AndreiCurea/C.H.A.R.L.E.S./3D Designs/Suport Motor.stl

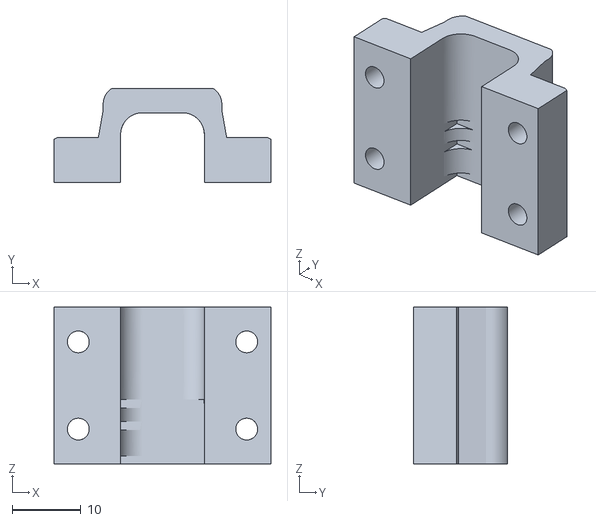
[picture p15: CAD file, 2023-12-22]
3D Designs/Suport Motor.stl
31.6 x 13.7 x 22.9
