AndreiCurea/C.H.A.R.L.E.S./3D Designs/Suport Separator Rulment.stl

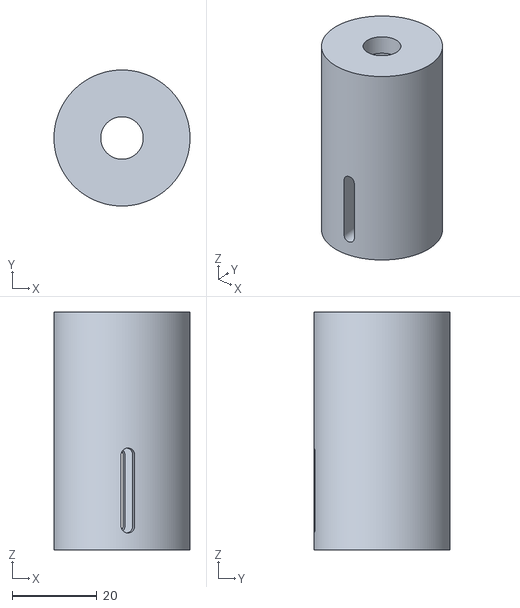
[picture p16: CAD file, 2023-12-22]
3D Designs/Suport Separator Rulment.stl
32.0 x 32.0 x 56.0
