AndreiCurea/C.H.A.R.L.E.S./3D Designs/Test_HCSR04.stl

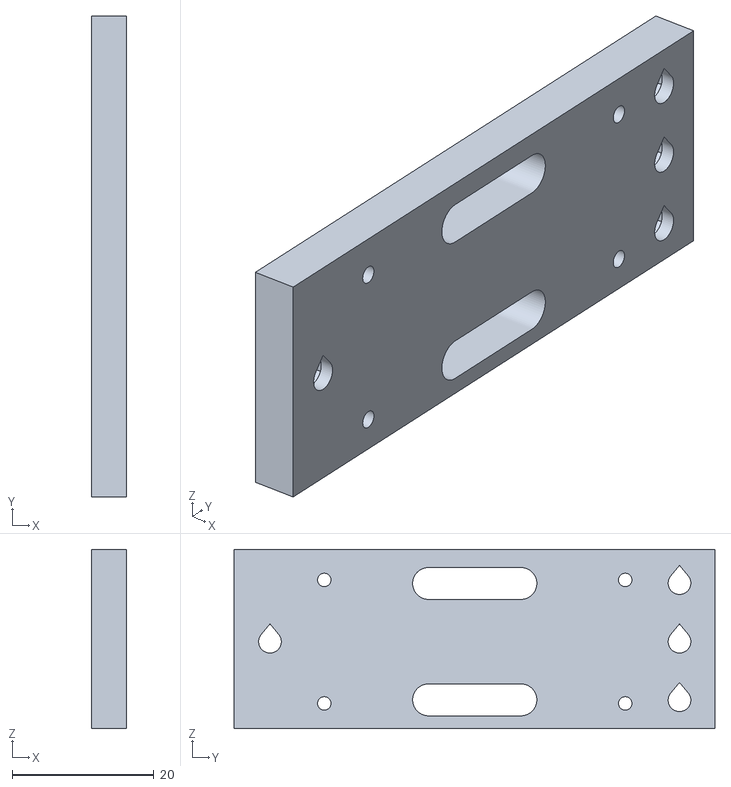
[picture p17: CAD file, 2023-12-22]
3D Designs/Test_HCSR04.stl
5.00 x 67.8 x 25.2
