AndreiCurea/C.H.A.R.L.E.S./3D Designs/Ziptie_Holder.stl

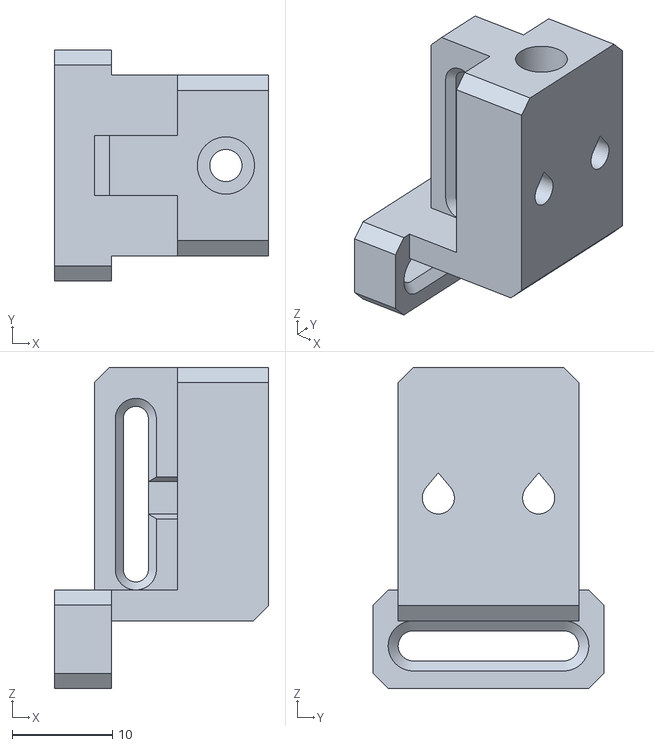
[picture p18: CAD file, 2023-12-22]
3D Designs/Ziptie_Holder.stl
21.4 x 23.0 x 32.0
