AndreiCurea/C.H.A.R.L.E.S./3D Designs/test_Gauri.stl

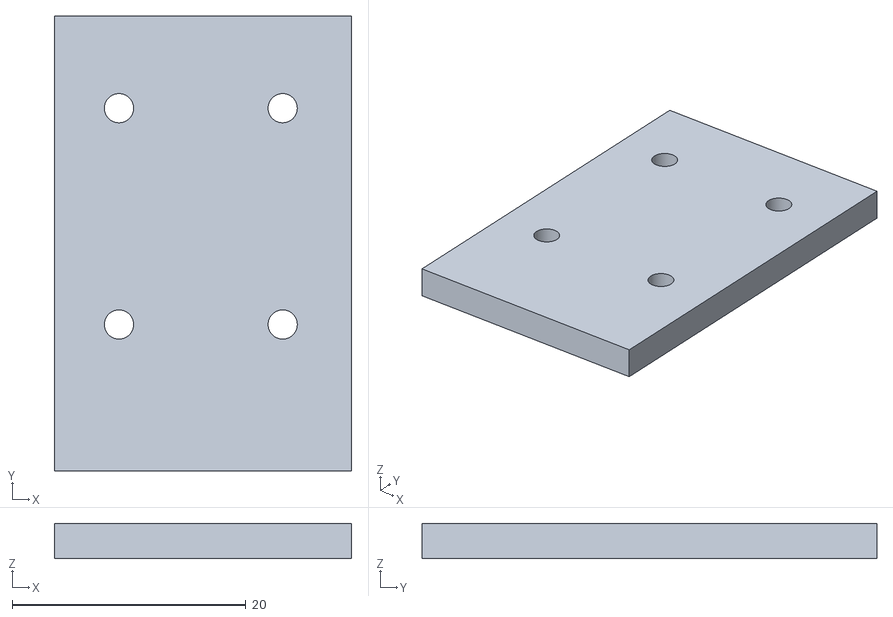
[picture p19: CAD file, 2023-12-22]
3D Designs/test_Gauri.stl
25.4 x 38.9 x 3.00
