AndreiCurea/C.H.A.R.L.E.S./3D Designs/Middle_Layer_2.stl

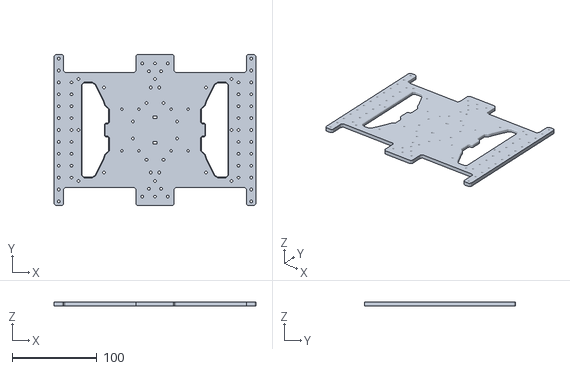
[picture p20: CAD file, 2023-12-22]
3D Designs/Middle_Layer_2.stl
237.7 x 178.0 x 5.00
