AndreiCurea/C.H.A.R.L.E.S./3D Designs/Suport_Battery_Level.stl

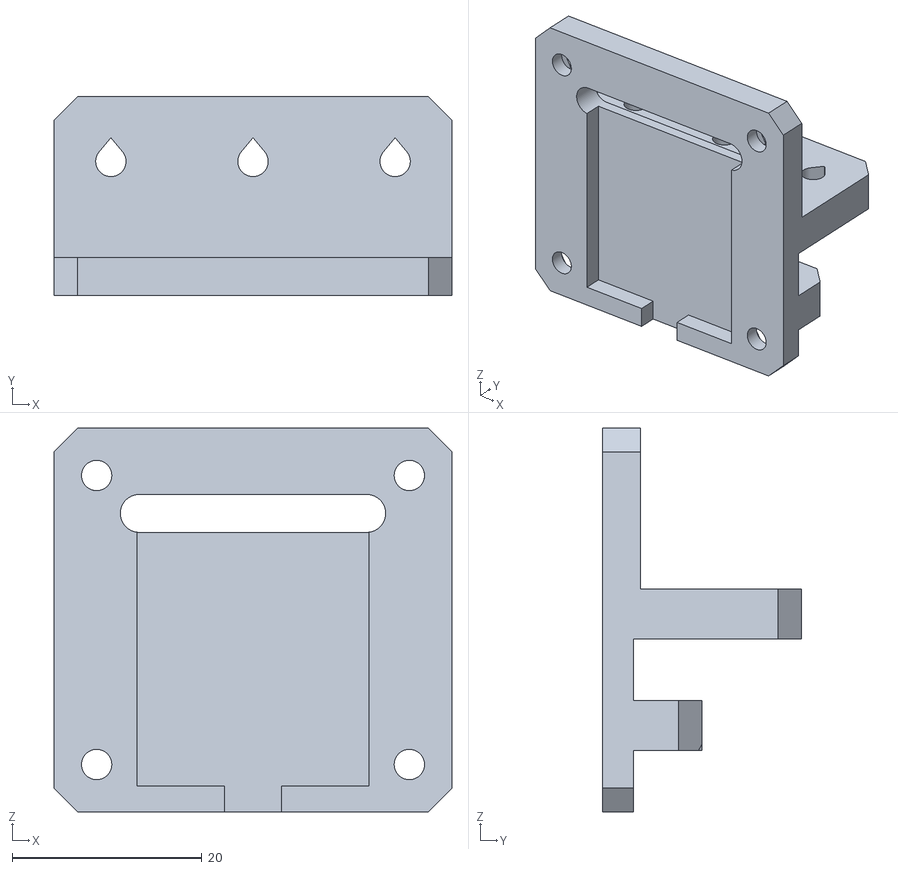
[picture p21: CAD file, 2023-12-22]
3D Designs/Suport_Battery_Level.stl
42.0 x 21.0 x 40.5
