AndreiCurea/C.H.A.R.L.E.S./3D Designs/Batt_ Conn_Dreapta.stl

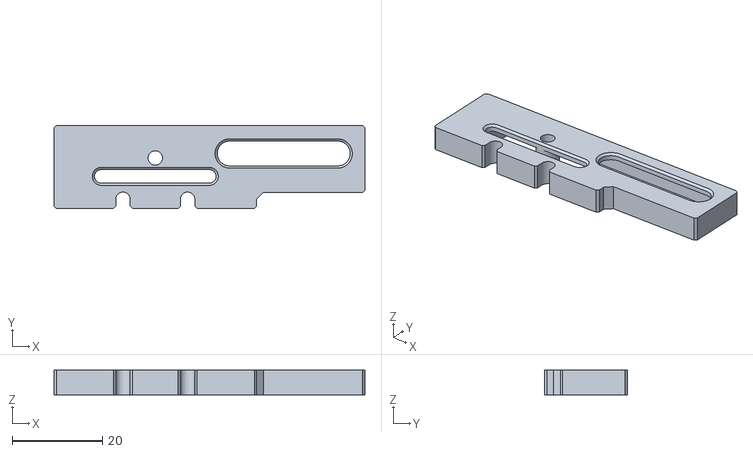
[picture p22: CAD file, 2023-12-22]
3D Designs/Batt_ Conn_Dreapta.stl
69.1 x 18.4 x 5.50
