AndreiCurea/C.H.A.R.L.E.S./3D Designs/Clips_Cuplaj_Mecanic.stl

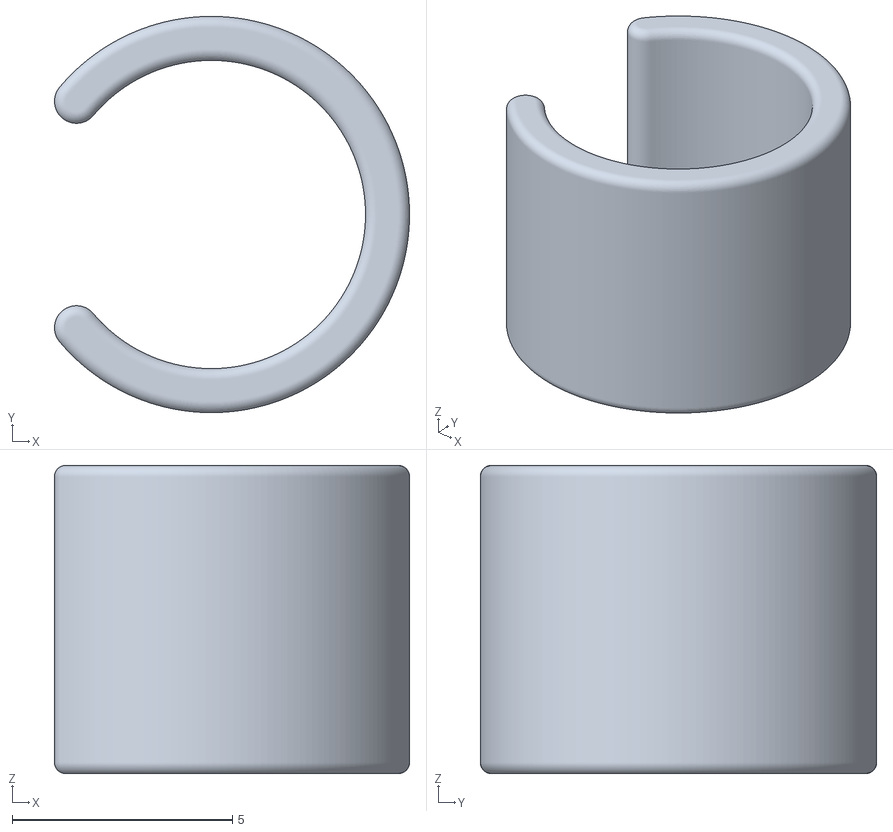
[picture p23: CAD file, 2023-12-22]
3D Designs/Clips_Cuplaj_Mecanic.stl
8.06 x 9.00 x 7.00
