AndreiCurea/C.H.A.R.L.E.S./3D Designs/Separator Rulment.stl

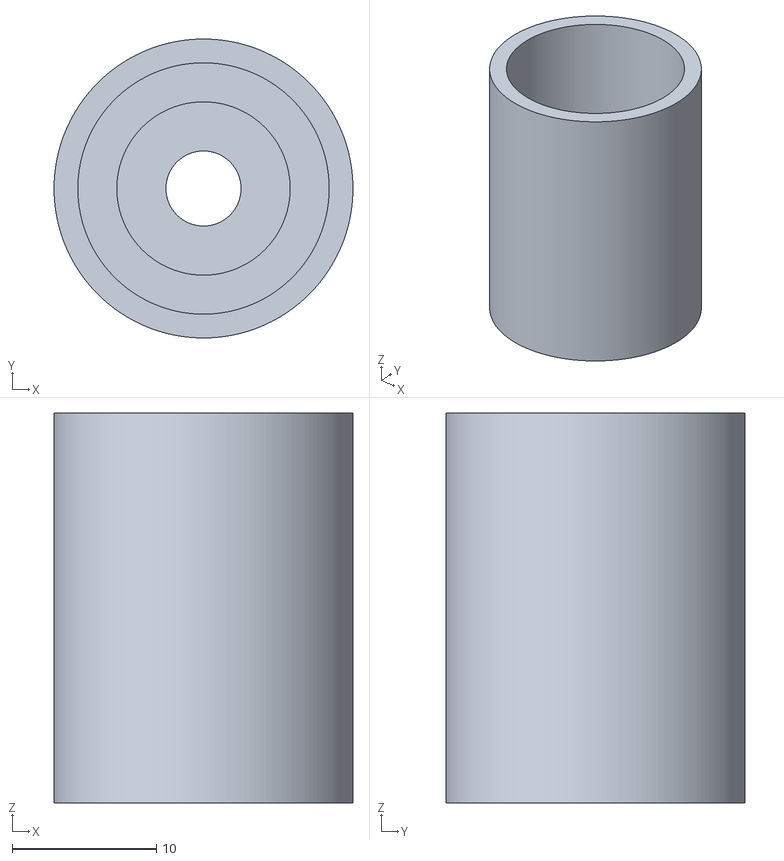
[picture p24: CAD file, 2023-12-22]
3D Designs/Separator Rulment.stl
20.7 x 20.7 x 27.0
