AndreiCurea/C.H.A.R.L.E.S./3D Designs/Test_Hole_Mot_Mount.stl

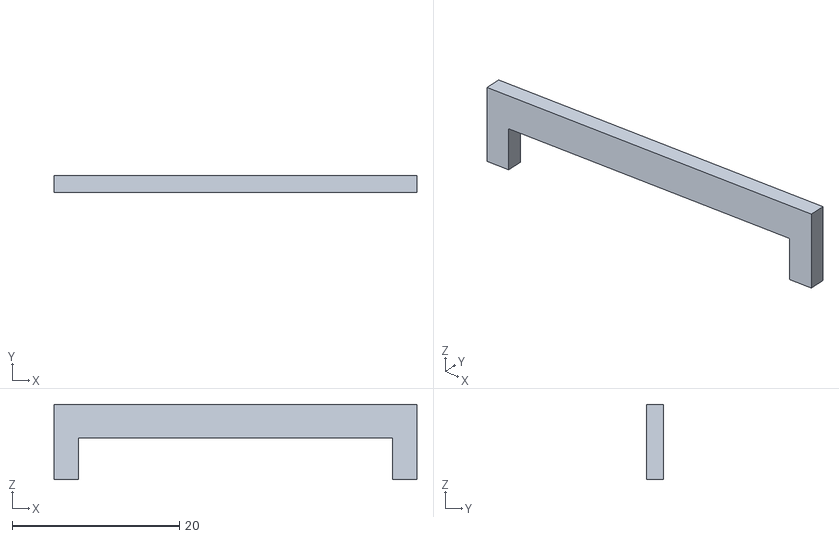
[picture p25: CAD file, 2023-12-22]
3D Designs/Test_Hole_Mot_Mount.stl
43.4 x 2.00 x 9.00
