AndreiCurea/C.H.A.R.L.E.S./3D Designs/TOP_Layer_3.stl

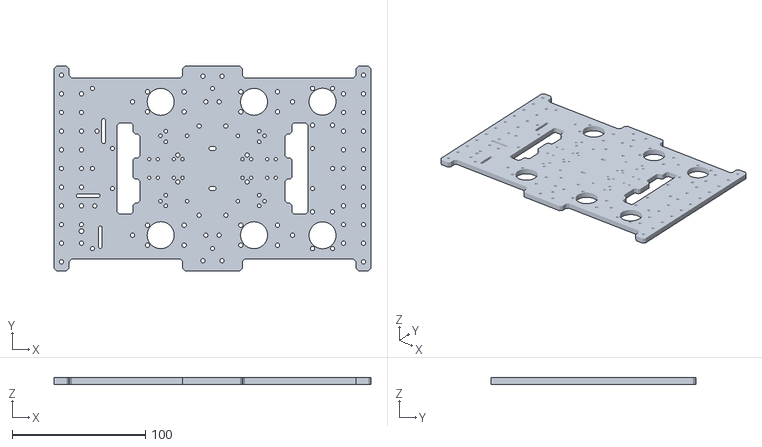
[picture p26: CAD file, 2023-12-22]
3D Designs/TOP_Layer_3.stl
237.7 x 153.5 x 5.00
