AndreiCurea/C.H.A.R.L.E.S./3D Designs/Test_Ins_Mot_Mount.stl

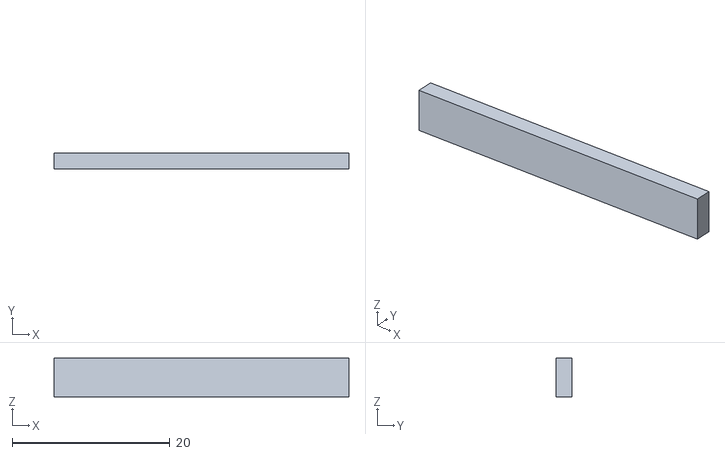
[picture p27: CAD file, 2023-12-22]
3D Designs/Test_Ins_Mot_Mount.stl
37.4 x 2.00 x 4.90
