AndreiCurea/C.H.A.R.L.E.S./3D Designs/Front_Support_Ultrasonic.stl

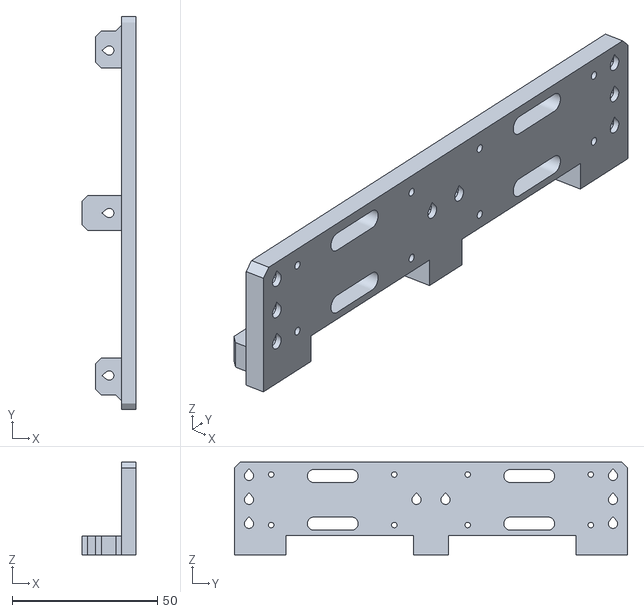
[picture p28: CAD file, 2023-12-22]
3D Designs/Front_Support_Ultrasonic.stl
18.7 x 135.4 x 32.0
